b00lduck/esp32-audioplayer/src/VS1053.cpp

/**
 * 
 * Copyright 2018 D.Zerlett <daniel@zerlett.eu>
 * 
 * This file is based on the VS1053 library by maniacbug alias J.Coliz (https://github.com/maniacbug/VS1053)
 * 
 * This file is part of esp32-audioplayer.
 * 
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
 */
#include <SPI.h>
#include "VS1053.h"
#include "tools.h"
#include "config.h"

VS1053::VS1053 (uint8_t _xcsPin, uint8_t _xdcsPin, uint8_t _dreqPin, uint8_t _xresetPin) : 
  xcsPin(_xcsPin), 
  xdcsPin(_xdcsPin), 
  dreqPin(_dreqPin), 
  xresetPin(_xresetPin) {}

uint16_t VS1053::read_register (uint8_t _reg) const {
  uint16_t result;
  controlModeOn();
  SPI.write(3);                                // Read operation
  SPI.write(_reg);                             // Register to write (0..0xF)
  // Note: transfer16 does not seem to work
  result = (SPI.transfer (0xFF) << 8) |         // Read 16 bits data
           (SPI.transfer (0xFF));
  await_data_request();                         // Wait for DREQ to be HIGH again
  controlModeOff();
  return result;
}

void VS1053::write_register (uint8_t _reg, uint16_t _value) const {
  controlModeOn();
  SPI.write(2);                                // Write operation
  SPI.write(_reg);                             // Register to write (0..0xF)
  SPI.write16(_value);                         // Send 16 bits data
  await_data_request();
  controlModeOff();
}

void VS1053::sdi_send_buffer (uint8_t* data, size_t len) {
  dataModeOn();
  while (len) {                                  // More to do?
    await_data_request();                         // Wait for space available
    size_t chunk_length = len;
    if (len > vs1053ChunkSize) {
      size_t chunk_length = vs1053ChunkSize;
    }
    len -= chunk_length;
    SPI.writeBytes (data, chunk_length);
    data += chunk_length;
  }
  dataModeOff();
}

void VS1053::sdi_send_fillers (size_t len) {
  dataModeOn();
  while (len) {                                  // More to do?
    await_data_request();                         // Wait for space available
    size_t chunk_length = len;
    if (len > vs1053ChunkSize) {
      chunk_length = vs1053ChunkSize;
    }
    len -= chunk_length;
    while (chunk_length--) {
      SPI.write (endFillByte);
    }
  }
  dataModeOff();
}

void VS1053::wram_write (uint16_t address, uint16_t data) {
  write_register (SCI_WRAMADDR, address);
  write_register (SCI_WRAM, data);
}

uint16_t VS1053::wram_read (uint16_t address) {
  write_register (SCI_WRAMADDR, address);            // Start reading from WRAM
  return read_register (SCI_WRAM);                   // Read back result
}

bool VS1053::testComm (const char *header) {
  // Test the communication with the VS1053 module.  The result wille be returned.
  // If DREQ is low, there is problably no VS1053 connected.  Pull the line HIGH
  // in order to prevent an endless loop waiting for this signal.  The rest of the
  // software will still work, but readbacks from VS1053 will fail.
  int       i;                                         // Loop control
  uint16_t  r1, r2, cnt = 0;
  uint16_t  delta = 300;                               // 3 for fast SPI

  if (!digitalRead (dreqPin)) {
    Serial.println ("VS1053 not properly installed!");
    // Allow testing without the VS1053 module
    pinMode (dreqPin,  INPUT_PULLUP);               // DREQ is now input with pull-up
    return false;                                      // Return bad result
  }
  // Further TESTING.  Check if SCI bus can write and read without errors.
  // We will use the volume setting for this.
  // Will give warnings on serial output if DEBUG is active.
  // A maximum of 20 errors will be reported.
  if (strstr (header, "Fast")) {
    delta = 3;                                         // Fast SPI, more loops
  }
  Serial.println (header);                                 // Show a header
  for (i = 0; (i < 0xFFFF) && (cnt < 20); i += delta) {
    write_register (SCI_VOL, i);                     // Write data to SCI_VOL
    r1 = read_register (SCI_VOL);                    // Read back for the first time
    r2 = read_register (SCI_VOL);                    // Read back a second time
    if  (r1 != r2 || i != r1 || i != r2)              // Check for 2 equal reads
    {
      Serial.printf ("VS1053 error retry SB:%04X R1:%04X R2:%04X\n", i, r1, r2);
      cnt++;
      delay (10);
    }
    yield();                                           // Allow ESP firmware to do some bookkeeping
  }
  return (cnt == 0);                                 // Return the result
}

void VS1053::begin() {  

  pinMode(dreqPin, INPUT);

  pinMode(xcsPin, OUTPUT);
  digitalWrite(xcsPin, HIGH);
  
  pinMode(xdcsPin, OUTPUT);
  digitalWrite(xdcsPin, HIGH);
  
  pinMode(xresetPin, OUTPUT);
  digitalWrite(xresetPin, HIGH);
     
  Serial.println ("Reset VS1053...");
  digitalWrite(xresetPin, LOW);
  delay(5); 
  Serial.println ("End reset VS1053...");
  digitalWrite(xresetPin, HIGH);
  
  // Init SPI in slow mode (0.2 MHz)
  VS1053_SPI = SPISettings (200000, MSBFIRST, SPI_MODE0);

  delay (20);
  testComm ("Slow SPI,Testing VS1053 read/write registers...");  

  // Most VS1053 modules will start up in midi mode.  The result is that there is no audio
  // when playing MP3.  You can modify the board, but there is a more elegant way:
  wram_write (0xC017, 3);                            // GPIO DDR = 3
  wram_write (0xC019, 0);                            // GPIO ODATA = 0
  delay (100);
    
   softReset();                                         
  
  // Power up analog circuits (44.1kHz stereo)
  write_register (SCI_AUDATA, 44100 + 1);
  
  // The next clock setting allows SPI clocking at 5 MHz, 4 MHz is safe then.
  write_register (SCI_CLOCKF, 6 << 12);  // Normal clock settings multiplier 3.0 = 12.2 MHz
  
  //SPI Clock to 4 MHz
  VS1053_SPI = SPISettings (4000000, MSBFIRST, SPI_MODE0);
  write_register (SCI_MODE, _BV (SM_SDINEW) | _BV (SM_LINE1));
  
  testComm ("Fast SPI, Testing VS1053 read/write registers again...");    
  delay(200);
  
  await_data_request();
  endFillByte = wram_read (0x1E06) & 0xFF;

  Serial.printf ("endFillByte is %X\n", endFillByte);
  delay (100);
}

void VS1053::setVolume (uint8_t vol) {
  // Set volume.  Both left and right.
  // Input value is 0..100.  100 is the loudest.
  // Clicking reduced by using 0xf8 to 0x00 as limits.
  uint16_t value;                                      // Value to send to SCI_VOL

  if (vol != curvol) {
    curvol = vol;                                      // Save for later use
    //value = map (vol, 0, 100, 0xF8, 0x00);           // 0..100% to one channel
    value = map (vol, 0, 100, 0x8f, 0x10);           // 0..100% to one channel
    value = (value << 8) | value;
    write_register (SCI_VOL, value);                 // Volume left and right
  }

  Serial.printf ("Volume %d\n", vol);
}

void VS1053::setTone (uint8_t *rtone) {               // Set bass/treble (4 nibbles)
  // Set tone characteristics.  See documentation for the 4 nibbles.
  uint16_t value = 0;                                  // Value to send to SCI_BASS
  int      i;                                          // Loop control
  for (i = 0; i < 4; i++) {
    value = (value << 4) | rtone[i];                 // Shift next nibble in
  }
  write_register (SCI_BASS, value);
}

uint8_t VS1053::getVolume() {
  return curvol;
}

void VS1053::startSong() {
  sdi_send_fillers (10);
}

void VS1053::playChunk (uint8_t* data, size_t len) {
  sdi_send_buffer (data, len);
}

void VS1053::stopSong() {
  uint16_t modereg;                     // Read from mode register
  int      i;                           // Loop control

  sdi_send_fillers (2052);
  delay (10);
  write_register (SCI_MODE, _BV (SM_SDINEW) | _BV (SM_CANCEL));
  for (i = 0; i < 200; i++) {
    sdi_send_fillers (32);
    modereg = read_register (SCI_MODE);  // Read status
    if ((modereg & _BV (SM_CANCEL)) == 0) {
      sdi_send_fillers (2052);
      Serial.printf("Song stopped correctly after %d ms\n", i * 10);
      return;
    }
    delay (10);
  }
  Serial.println("Song stopped incorrectly!");
  printDetails ();
}

void VS1053::softReset() {
  write_register (SCI_MODE, _BV (SM_SDINEW) | _BV (SM_RESET));
  delay (10);
  await_data_request();
}

void VS1053::processByte (uint8_t b, bool force) {
  chunkbuf[chunkbufcnt++] = b;
  if (chunkbufcnt == sizeof(chunkbuf) || force) {             
    playChunk (chunkbuf, chunkbufcnt);           
    chunkbufcnt = 0;            
  }
  return;    
}

void VS1053::printDetails () {
  Serial.println("VS1053 register dump:");
  Serial.println("REG   Contents");
  Serial.println("---   --------");
  for (uint8_t i = 0; i <= SCI_num_registers; i++) {
    Serial.printf("%3x - %5x\n", i, read_register(i));
  }
}
