b00lduck/esp32-audioplayer/src/player.cpp

/**
 * 
 * Copyright 2018 D.Zerlett <daniel@zerlett.eu>
 * 
 * This file is part of esp32-audioplayer.
 * 
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
 */
#include "config.h"
#include "player.h"
#include "VS1053.h"
#include <SD.h>

  Player::Player(Fatal fatal, Oled oled, VS1053 vs1053) : 
      state(STOPPED), 
      oldState(INITIALIZING),
      fatal(fatal),     
      #ifdef OLED
        oled(oled),
      #endif
      vs1053(vs1053),
      ringBuffer(20000),
      dataFile(),
      currentVolume(65),      
      lastTime(0),
      idleTime(0) {}

void Player::init() {
  // Initialize audio decoder
  vs1053.begin();
  #ifndef FAST_BOOT
    vs1053.printDetails();
  #endif
}

void Player::play(char* filename) {

  Serial.printf("Play: %s\n", filename);

  clearPlaylist();

  dataFile = SD.open(filename, FILE_READ);
  if (!dataFile) {
    Serial.printf("Error opening file %s\n", filename);
    dataFile = SD.open("/error.mp3", FILE_READ);
    if (!dataFile) {
      stop();
      return;
    }
  }

  if (dataFile.isDirectory()) {
    // read directory into playlist

    Serial.printf("%s is a directory, creating playlist...\n", filename);
    clearPlaylist();

    File file = dataFile.openNextFile();    
    while (file && playlistLen+1 < MAX_PLAYLIST_LENGTH) {
      if(!file.isDirectory()){
        Serial.printf("Track %02d: %s\n", playlistLen, file.name());
        addPlaylistEntry((char*) file.name());
      }   
      file = dataFile.openNextFile();
    }

    Serial.printf("Playlist has %d items.\n", playlistLen);

  } else {
    addPlaylistEntry(filename);
  } 

  playNextFile();
}

void Player::addPlaylistEntry(char* filename) {
    playlist[playlistLen] = (char*) malloc(MAX_FILENAME_LENGTH);
    strncpy(playlist[playlistLen], filename, MAX_FILENAME_LENGTH);
    playlistLen++;
}

void Player::clearPlaylist() {
  for(uint8_t i=0; i<playlistLen; i++) {
    free(playlist[i]);
  }
  playlistLen = 0;
  playlistIndex = 0;
}

void Player::playNextFile() {

  if (playlistLen == 0) {
    stop();   
  }

  Serial.printf("Playing next file in playlist (%d/%d)\n", playlistIndex + 1, playlistLen);

  digitalWrite(AMP_ENABLE, HIGH);  // enable amplifier
  digitalWrite(LED2, HIGH);
  
  char* filename = playlist[playlistIndex];

  Serial.printf("Filename: %s\n", filename);

  dataFile = SD.open(filename, FILE_READ);
  if (!dataFile) {
    next();
  }

  // skip ID3v2 tag if present
  uint8_t header[10];
  dataFile.read(header, 10);
  if ((header[0] == 'I') && (header[1] == 'D') && (header[2] == '3')) {    
    uint32_t header_size = header[9] + ((uint16_t)header[8] << 7) + ((uint32_t)header[7] << 14) + ((uint32_t)header[6] << 21);
    Serial.printf("Found ID3v2 tag at beginning, skipping %d bytes\n", header_size);
    dataFile.seek(header_size);    
  } else {
    dataFile.seek(0);
  }  

  delay(300);

  state = PLAYING;
  vs1053.setVolume(currentVolume);                 

  uint8_t tone[4] = {0,0,15,15};
  vs1053.setTone(tone);
}

void Player::next() {
  if (playlistIndex + 1 < playlistLen) {
    playlistIndex++;
    playNextFile();
  } else {
    stop();
  }
}

void Player::stop() {  
  digitalWrite(AMP_ENABLE, LOW);  // disable amplifier
  digitalWrite(LED2, LOW);
  dataFile.close();
  vs1053.processByte(0, true);
  vs1053.setVolume(0);                  
  vs1053.stopSong();                       
  ringBuffer.empty();                            
  state = STOPPED; 
  clearPlaylist();
}

void Player::process() {

  uint32_t maxfilechunk;

  if (oldState != state) {
    Serial.printf("Player state is now %d, was %d.\n", state, oldState);
    oldState = state;
  }
         
  uint32_t timeGone = millis() - lastTime;

  switch (state) {

    case PLAYING:      
      // fill ring buffer with MP3 data
      maxfilechunk = dataFile.available();
      if (maxfilechunk > 1024) {
        maxfilechunk = 1024;      
      }
      while (ringBuffer.space() && maxfilechunk--) {
        ringBuffer.put(dataFile.read());
      } 
      
      // Try to keep VS1053 filled
      while (vs1053.data_request() && ringBuffer.avail()) { 
        vs1053.processByte(ringBuffer.get(), false);
      }

      // stop if data ends
      if ((dataFile.available() == 0) && (ringBuffer.avail() == 0)) {      
        next();
      }
      idleTime = 0;
      break;

    case STOPPED:
      #ifdef OLED
        oled.trackName("");
      #endif
      idleTime += timeGone;
      break;    
    
  }
}

void Player::setVolume(uint8_t volume) {
  currentVolume = volume;
  if (currentVolume > 100) {
    currentVolume = 100;
  }
  if (currentVolume < 1) {
    currentVolume = 1;
  }
  oled.volumeBar(currentVolume);
  vs1053.setVolume(currentVolume);
 }

void Player::increaseVolume() {
    setVolume(currentVolume+1);
}

void Player::decreaseVolume() {
    setVolume(currentVolume-1);
}
