b00lduck/esp32-audioplayer/src/rfid.cpp

/**
 * 
 * Copyright 2018 D.Zerlett <daniel@zerlett.eu>
 * 
 * This file is part of esp32-audioplayer.
 * 
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
 */
#include "rfid.h"
#include "tools.h"

RFID::RFID(uint8_t _csPin, uint8_t _rstPin) : 
  csPin(_csPin),
  rstPin(_rstPin),
  mfrc522(csPin,rstPin)
  {}

void RFID::init() {
   mfrc522.PCD_Init();  
   mfrc522.PCD_DumpVersionToSerial(); 
  // mfrc522.PCD_SetAntennaGain(mfrc522.RxGain_max);
}

RFID::CardState RFID::checkCardState() {
  
  if (mfrc522.PICC_IsNewCardPresent()) {
    if (mfrc522.PICC_ReadCardSerial()) {
      cardFailCount = 0;    
      if (cardChanged(mfrc522.uid.uidByte, mfrc522.uid.size)) {
        newCard(mfrc522.uid.uidByte, mfrc522.uid.size);        
        return CardState::NEW_CARD;        
      }      
    } else {
        Serial.println(F("Error reading card"));
        cardPresent = false;   
        return CardState::FAULTY_CARD;                   
    }
  } else {
    if (cardPresent) {
      cardFailCount++;
      if (cardFailCount > 1) {
          Serial.println(F("Card removed"));
          cardPresent = false;   
          memset(currentCard, 0, sizeof(currentCard));
          return CardState::REMOVED_CARD;                 
      }     
    }
  } 

   return CardState::NO_CHANGE;
}

/** 
 * compares buffer with the currently active card  
 * return true if card ID has changed
 */
bool RFID::cardChanged(byte *buffer, byte bufferSize) {
  for (uint8_t i = 0; i < bufferSize; i++) {
    if (buffer[i] != currentCard[i]) {
      return true;
    }
  }
  return false;
}

/**
 * called when a new card is detected
 */
void RFID::newCard(byte *buffer, byte bufferSize) {
  cardPresent = true;
  if (bufferSize > sizeof(currentCard)) {
    bufferSize = sizeof(currentCard);
  }
  memcpy(currentCard, buffer, bufferSize);
  Serial.print(F("New Card with UID"));
  dumpByteArray(mfrc522.uid.uidByte, mfrc522.uid.size);  
  Serial.println(F(" detected."));  
}
